soemarko/whey/Sketch/v2/espnow-sender/espnow-sender.ino

#include <esp_now.h>
#include <WiFi.h>

// REPLACE WITH YOUR RECEIVER MAC Address
uint8_t broadcastAddress[] = {0x4C, 0x11, 0xAE, 0xA5, 0xF3, 0x1C};

// Structure example to send data
// Must match the receiver structure
typedef struct struct_message {
    long value;
} struct_message;


// Create a struct_message called myData
struct_message myData;
 
void setup() {
  // Init Serial Monitor
  Serial.begin(115200);
 
  // Set device as a Wi-Fi Station
  WiFi.mode(WIFI_STA);

  // Init ESP-NOW
  if (esp_now_init() != ESP_OK) {
    Serial.println("Error initializing ESP-NOW");
    return;
  }
  
  // Register peer
  esp_now_peer_info_t peerInfo;
  memcpy(peerInfo.peer_addr, broadcastAddress, 6);
  peerInfo.channel = 0;  
  peerInfo.encrypt = false;
  
  // Add peer        
  if (esp_now_add_peer(&peerInfo) != ESP_OK){
    Serial.println("Failed to add peer");
    return;
  }
  
  randomSeed(analogRead(0));
}
 
void loop() {
  // Set values to send

  myData.value = random(2147483647);

  // Send message via ESP-NOW
  esp_err_t result = esp_now_send(broadcastAddress, (uint8_t *) &myData, sizeof(myData));
   
  if (result == ESP_OK) {
    Serial.println("Sent with success");
  }
  else {
    Serial.println("Error sending the data");
  }

  delay(250);
}
